italorosq/thrust-stand/docs/imagens/caixa_v1_lateral_superior.jpg

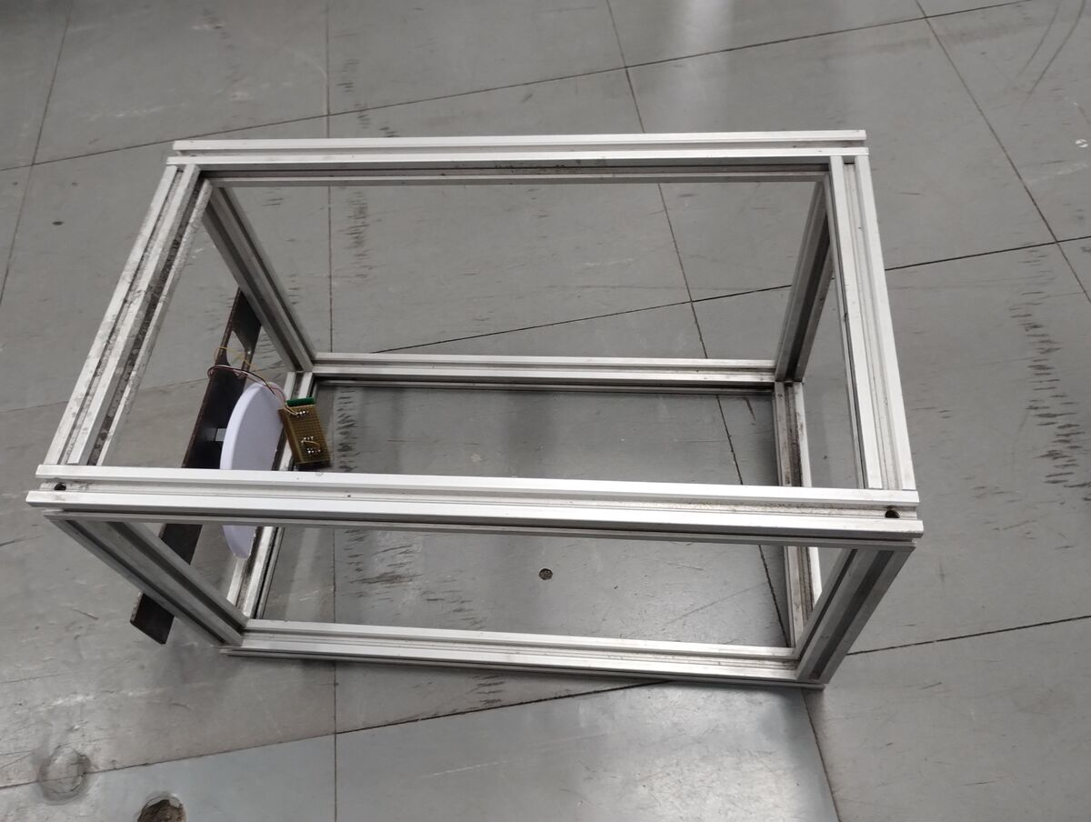
docs/imagens/caixa_v1_lateral_superior.jpg
